martinberlin/H-C6-ulp/components/3D/JST_SM02B-SRSS-TB__LF__SN.stp

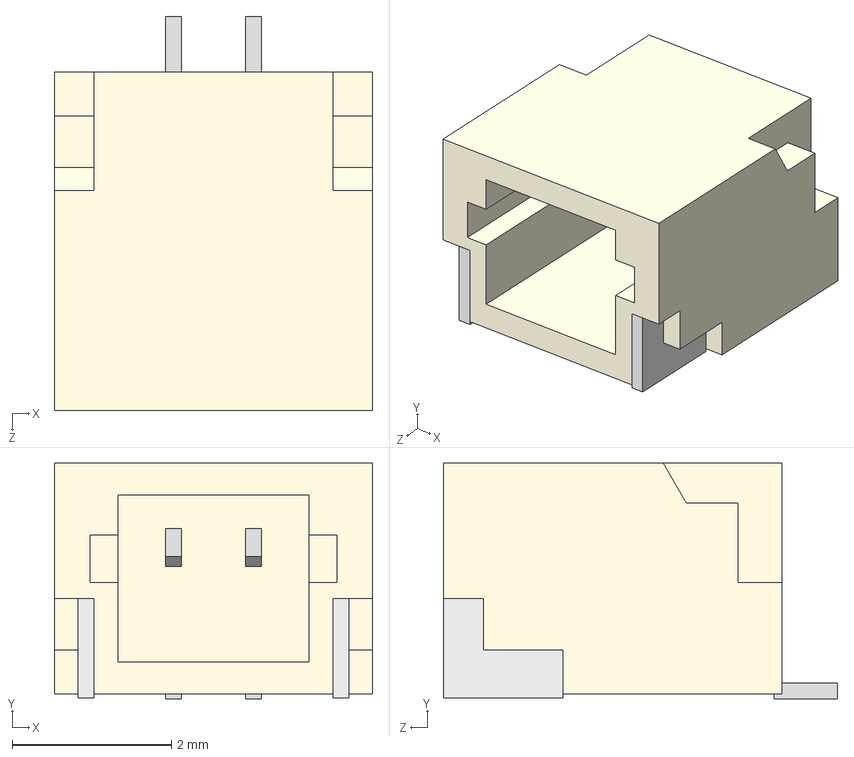
[picture p19: CAD file, 2024-09-13]
components/3D/JST_SM02B-SRSS-TB__LF__SN.stp
4.00 x 2.96 x 4.95 mm
