martinberlin/H-C6-ulp/components/3D/RV-3032-C7.stp

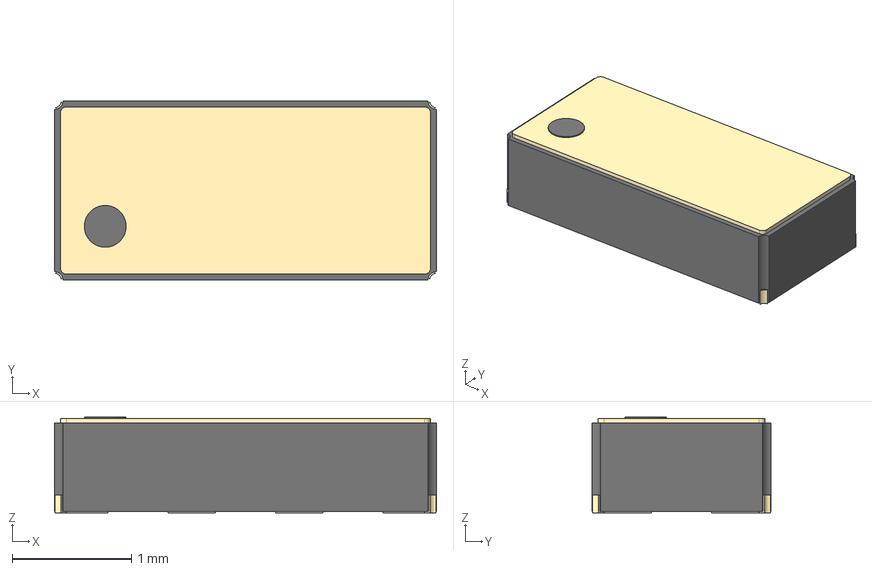
[picture p20: CAD file, 2024-09-13]
components/3D/RV-3032-C7.stp
3.20 x 1.50 x 0.8 mm
Rect2
Rect3
Rect4
Rect5
Terminal
