martinberlin/H-C6-ulp/components/3D/FH12-24S-0.5SH_55_.step

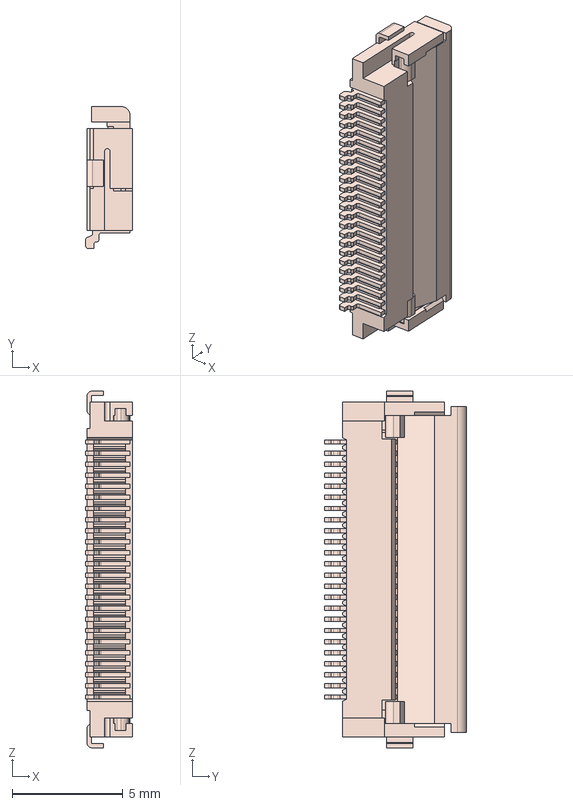
[picture p21: CAD file, 2024-09-10]
components/3D/FH12-24S-0.5SH_55_.step
2.10 x 6.40 x 16.1 mm
