martinberlin/H-C6-ulp/components/3D/2450AT42E0100E-ANT.stp

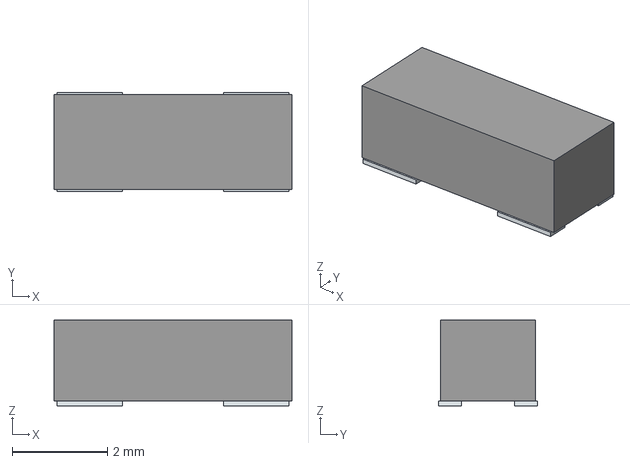
[picture p22: CAD file, 2024-09-10]
components/3D/2450AT42E0100E-ANT.stp
5.00 x 2.08 x 1.80 mm
Pins
