martinberlin/H-C6-ulp/components/3D/USB_TYPE-C-31-M-12.step

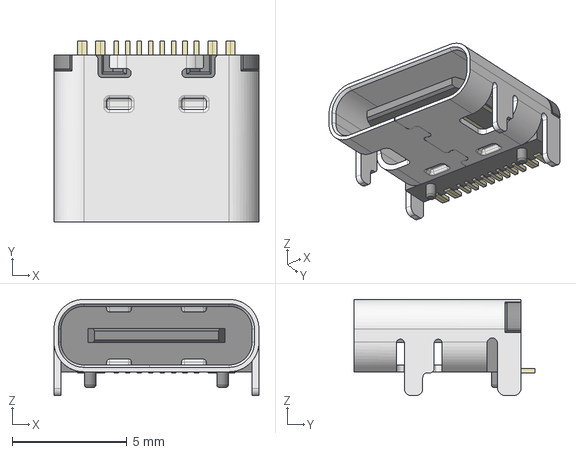
[picture p23: CAD file, 2024-09-10]
components/3D/USB_TYPE-C-31-M-12.step
8.95 x 7.90 x 4.20 mm
