martinberlin/H-C6-ulp/components/3D/ESP32-C6.stp

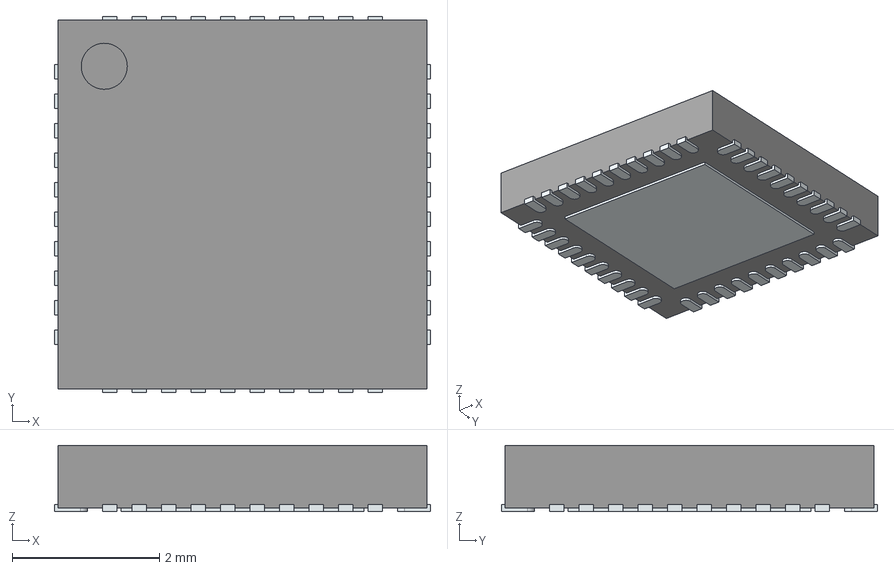
[picture p24: CAD file, 2024-09-10]
components/3D/ESP32-C6.stp
5.10 x 5.10 x 0.9 mm
ThermalPin
PinsArrayLR
PinsArrayTB
