martinberlin/H-C6-ulp/components/3D/Crytal_ECS-40Mhz_ECS.step

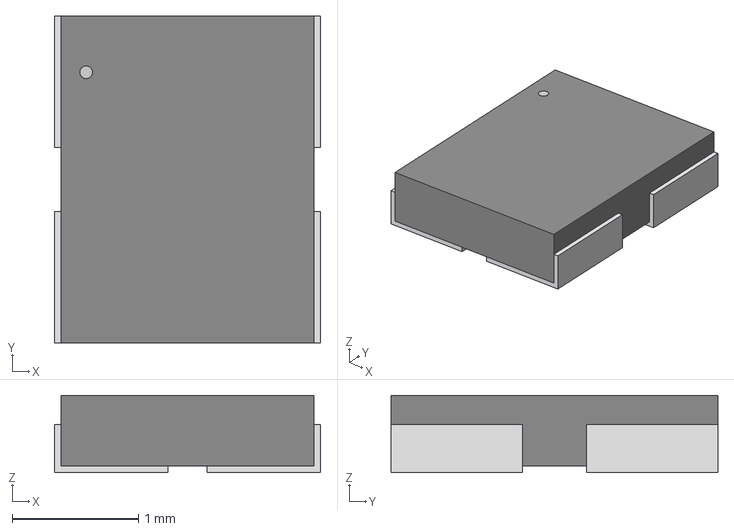
[picture p25: CAD file, 2024-09-10]
components/3D/Crytal_ECS-40Mhz_ECS.step
2.11 x 2.59 x 0.612 mm
