martinberlin/H-C6-ulp/components/3D/SGM6029_WLCSP-6_L1.0-W0.7.step

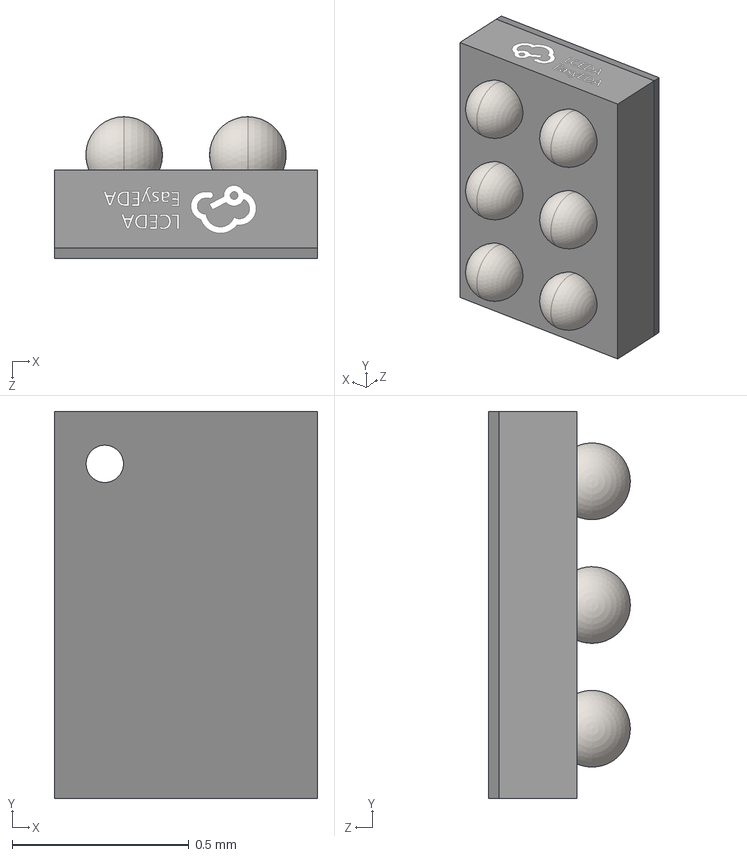
[picture p26: CAD file, 2024-09-10]
components/3D/SGM6029_WLCSP-6_L1.0-W0.7.step
0.745 x 1.10 x 0.401 mm
